AradhittaGoenka/Chameleon-skirt/Source files/Images/Colour sensor black RGB values.jpg7.jpg

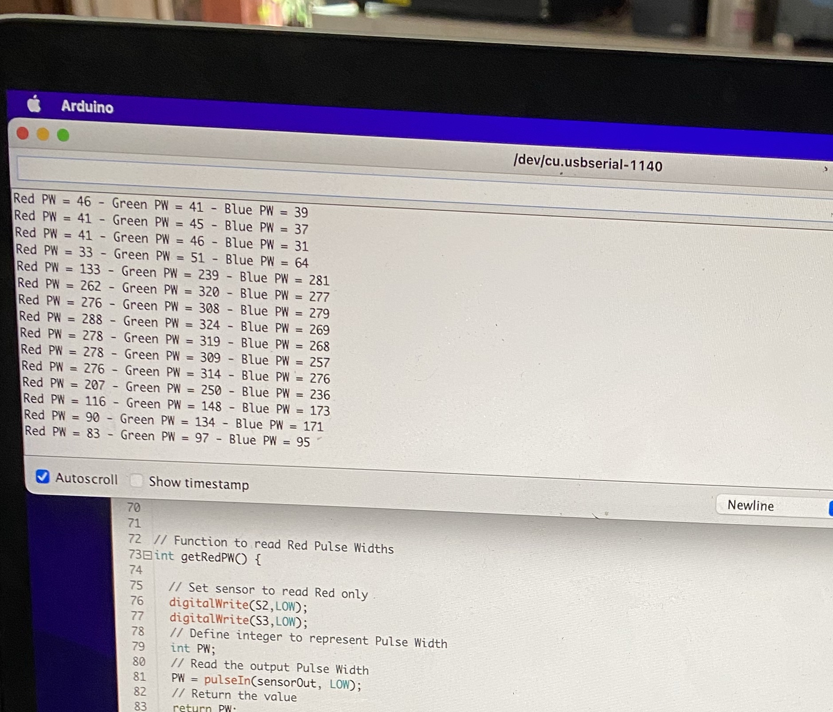
Source files/Images/Colour sensor black RGB values.jpg7.jpg
